slawyn/temperature-sensor/simulation/Differential.asc

100: res; 1000
C1: cap; 100n
C2: cap; 1.2µ; V=50 Irms=3.8 Rser=0 Lser=0
C3: cap; 1µ
C4: cap; 1µ
D1: TVSdiode; SMBJ24CA
Q1: npn
R1: res; 100
R2: res; 100
R3: res; 1000
R4: res; 100
R5: res; 10000
R6: res; 1k
R7: res; 1k
R8: res; 120
R9: res; 1k
R11: res; 1k
R12: res; 1k
U1: OP07
V1: voltage; PULSE(0 2 0 0.001 0.001 1 2)
V2: voltage; -5
V3: voltage; 5
V4: voltage; 3.5
V5: voltage; PULSE(0 5 1 0 0 2)
V6: voltage; PULSE(0 -5 1 0 0 2)
V7: voltage; PULSE(0 300 2 0.001 0.001 0.001)
V8: voltage; SINE(5 5 500 0 0 30 500)
Named nets: 0, Supply
.tran 2
