slawyn/temperature-sensor/simulation/npn.asc

Q1: pnp
R1: res; 1k
R2: res; 10k
R3: res; 50
V1: voltage; 0
V2: voltage; 3.3
Named nets: 0
.tran 1
