slawyn/temperature-sensor/firmware/firmware-v2/thermos.X/configbits.h

/* Microchip Technology Inc. and its subsidiaries.  You may use this software 
 * and any derivatives exclusively with Microchip products. 
 * 
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
 * IN NO EVENT WILL MICROCHIP BE LIABLE FOR ANY INDIRECT, SPECIAL, PUNITIVE, 
 * INCIDENTAL OR CONSEQUENTIAL LOSS, DAMAGE, COST OR EXPENSE OF ANY KIND 
 * WHATSOEVER RELATED TO THE SOFTWARE, HOWEVER CAUSED, EVEN IF MICROCHIP HAS 
 * BEEN ADVISED OF THE POSSIBILITY OR THE DAMAGES ARE FORESEEABLE.  TO THE 
 * FULLEST EXTENT ALLOWED BY LAW, MICROCHIP'S TOTAL LIABILITY ON ALL CLAIMS 
 * IN ANY WAY RELATED TO THIS SOFTWARE WILL NOT EXCEED THE AMOUNT OF FEES, IF 
 * ANY, THAT YOU HAVE PAID DIRECTLY TO MICROCHIP FOR THIS SOFTWARE.
 *
 * MICROCHIP PROVIDES THIS SOFTWARE CONDITIONALLY UPON YOUR ACCEPTANCE OF THESE 
 * TERMS. 
 */

/* 
 * File:   
 * Author: 
 * Comments:
 * Revision history: 
 */

// This is a guard condition so that contents of this file are not included
// more than once.  
#ifndef XC_HEADER_TEMPLATE_H
#define	XC_HEADER_TEMPLATE_H

// PIC24FJ128GL302 Configuration Bit Settings
// 'C' source line config statements
// FSEC
#pragma config BWRP = OFF               // Boot Segment Write-Protect bit (Boot Segment may be written)
#pragma config BSS = DISABLED           // Boot Segment Code-Protect Level bits (No Protection (other than BWRP))
#pragma config BSEN = OFF               // Boot Segment Control bit (No Boot Segment)
#pragma config GWRP = OFF               // General Segment Write-Protect bit (General Segment may be written)
#pragma config GSS = DISABLED           // General Segment Code-Protect Level bits (No Protection (other than GWRP))
#pragma config CWRP = OFF               // Configuration Segment Write-Protect bit (Configuration Segment may be written)
#pragma config CSS = DISABLED           // Configuration Segment Code-Protect Level bits (No Protection (other than CWRP))
#pragma config AIVTDIS = OFF            // Alternate Interrupt Vector Table bit (Disabled AIVT)

// FBSLIM
#pragma config BSLIM = 0x1FFF           // Boot Segment Flash Page Address Limit bits (Enter Hexadecimal value)

// FOSCSEL
#pragma config FNOSC = OSCFDIV          // Oscillator Source Selection (Oscillator with Divider)
#pragma config PLLMODE = DISABLED       // PLL Mode Selection (No PLL used; PLLEN bit is not available)
#pragma config IESO = ON                // Two-speed Oscillator Start-up Enable bit (Start up device with FRC, then switch to user-selected oscillator source)

// FOSC
#pragma config POSCMD = NONE            // Primary Oscillator Mode Select bits (Primary Oscillator disabled)
#pragma config OSCIOFCN = OFF           // OSC2 Pin Function bit (OSC2 is clock output)
#pragma config SOSCSEL = ON             // SOSC Power Selection Configuration bits (SOSC is used in crystal (SOSCI/SOSCO) mode)
#pragma config PLLSS = PLL_PRI          // PLL Secondary Selection Configuration bit (PLL is fed by the Primary oscillator)
#pragma config IOL1WAY = ON             // Peripheral pin select configuration bit (Allow only one reconfiguration)
#pragma config FCKSM = CSDCMD           // Clock Switching Mode bits (Both Clock switching and Fail-safe Clock Monitor are disabled)

// FWDT
#pragma config WDTPS = PS32768          // Watchdog Timer Postscaler bits (1:32,768)
#pragma config FWPSA = PR128            // Watchdog Timer Prescaler bit (1:128)
#pragma config FWDTEN = OFF             // Watchdog Timer Enable bits (WDT Disabled)
#pragma config WINDIS = OFF             // Watchdog Timer Window Enable bit (Watchdog Timer in Non-Window mode)
#pragma config WDTWIN = WIN25           // Watchdog Timer Window Select bits (WDT Window is 25% of WDT period)
#pragma config WDTCMX = WDTCLK          // WDT MUX Source Select bits (WDT clock source is determined by the WDTCLK Configuration bits)
#pragma config WDTCLK = LPRC            // WDT Clock Source Select bits (WDT uses LPRC)

// FPOR
#pragma config BOREN = ON               // Brown Out Enable bit (Brown Out Enable Bit)
#pragma config LPCFG = OFF              // Low power regulator control (No Retention Sleep)
#pragma config DNVPEN = ENABLE          // Downside Voltage Protection Enable bit (Downside protection enabled using ZPBOR when BOR is inactive)

// FICD
#pragma config ICS = PGD2               // ICD Communication Channel Select bits (Communicate on PGEC2 and PGED2)
#pragma config JTAGEN = OFF             // JTAG Enable bit (JTAG is disabled)

// FDMTIVTL
#pragma config DMTIVTL = 0xFFFF         // Deadman Timer Interval Low Word (Enter Hexadecimal value)

// FDMTIVTH
#pragma config DMTIVTH = 0xFFFF         // Deadman Timer Interval High Word (Enter Hexadecimal value)

// FDMTCNTL
#pragma config DMTCNTL = 0xFFFF         // Deadman Timer Instruction Count Low Word (Enter Hexadecimal value)

// FDMTCNTH
#pragma config DMTCNTH = 0xFFFF         // Deadman Timer Instruction Count High Word (Enter Hexadecimal value)

// FMDT
#pragma config DMTDIS = OFF             // Deadman Timer Enable Bit (Dead Man Timer is Disabled and can be enabled by software)

// FDEVOPT1
#pragma config ALTCMPI = DISABLE        // Alternate Comparator Input Enable bit (C2INC and C3INC are on their standard pin locations )
#pragma config TMPRPIN = OFF            // Tamper Pin Enable bit (TMPRN pin function is disabled)
#pragma config SOSCHP = ON              // SOSC High Power Enable bit (valid only when SOSCSEL = 1 (Enable SOSC high power mode (default))
#pragma config ALTI2C1 = ALTI2C1_OFF    // Alternate I2C pin Location (I2C1 Pin mapped to SDA1/SCL1 pins)
#pragma config SMB3EN = SMBUS3          // SM Bus Enable (SMBus 3.0 input levels)


#endif	/* XC_HEADER_TEMPLATE_H */
